SamirChamanSerna/V0.2_Nozzle_Wiper/Images/20240901_215018.jpg

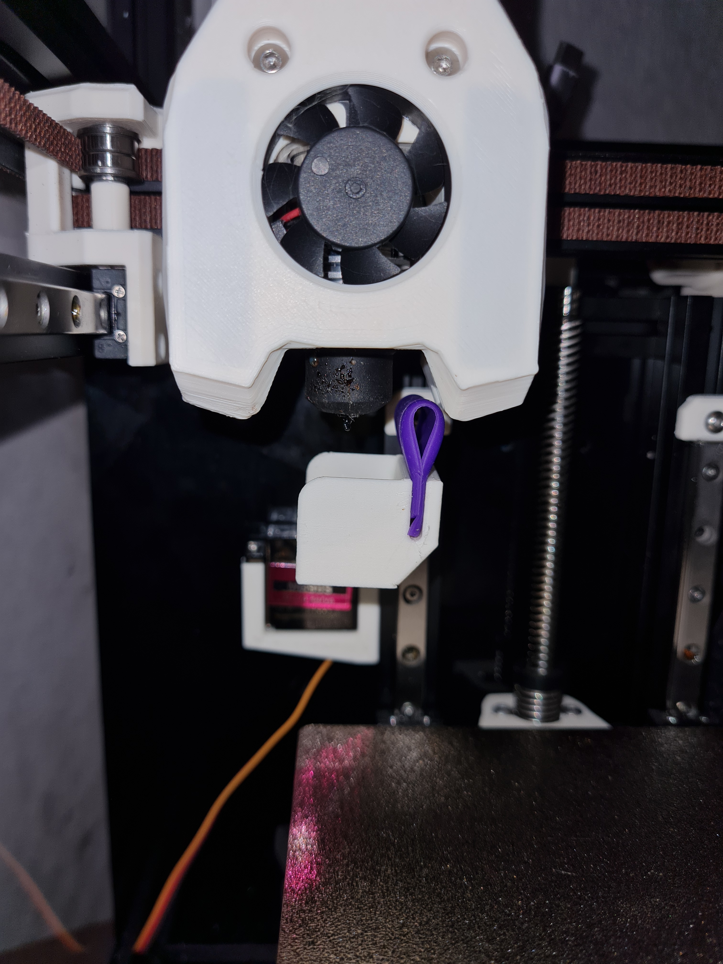
Images/20240901_215018.jpg
