SamirChamanSerna/V0.2_Nozzle_Wiper/Images/20240901_215220.jpg

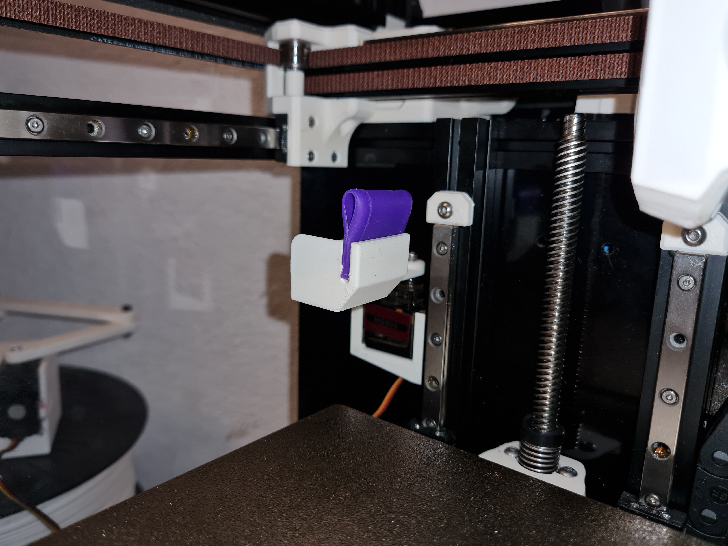
Images/20240901_215220.jpg
